CircuitMonkey/epoch-3/Firmware/epoch-3-fw/glyphs.h

#include <sys/_stdint.h>
// [glyph16g]  glyph  16x16   greyscale  as nybles
#ifndef Glyphs_h 
#define Glyphs_h

#define LOGO_W 128
#define LOGO_H 88
#define GLYPH_WH 64

#define PROGMEM

const uint8_t logo[] PROGMEM = { // 128 x 88 1-bit logo
  0x00,0x00,0x00,0x00,0x00,0x00,0x00,0x00,0x00,0x00,0x00,0x00,0x00,0x00,0x00,0x00
  ,0x00,0x00,0x00,0x00,0x00,0x00,0x00,0x00,0x00,0x00,0x00,0x00,0x00,0x00,0x00,0x00
  ,0x00,0x00,0x00,0x00,0x00,0x00,0x00,0x00,0x00,0x00,0x00,0x00,0x00,0x00,0x00,0x00
  ,0x00,0x00,0x00,0x00,0x00,0x00,0x00,0x00,0x00,0x00,0x00,0x00,0x00,0x00,0x00,0x00
  ,0x00,0x00,0x00,0x00,0x00,0x00,0x00,0x00,0x00,0x00,0x00,0x00,0x00,0x00,0x00,0x00
  ,0x00,0x00,0x00,0x00,0x00,0x00,0x00,0x00,0x00,0x00,0x00,0x00,0x00,0x00,0x00,0x00
  ,0x00,0x00,0x00,0x00,0x00,0x00,0x00,0x00,0x00,0x00,0x00,0x00,0x00,0x00,0x00,0x00
  ,0x00,0x00,0x00,0x00,0x00,0x00,0x00,0x00,0x00,0x00,0x00,0x00,0x00,0x00,0x00,0x00
  ,0x00,0x00,0x00,0x00,0x00,0x00,0x00,0x00,0x00,0x00,0x00,0x00,0x00,0x00,0x00,0x00
  ,0x00,0x00,0x00,0x00,0x00,0x00,0x00,0x00,0x00,0x00,0x00,0x00,0x00,0x00,0x00,0x00
  ,0x00,0x00,0x00,0x00,0x00,0x00,0x00,0x00,0x00,0x00,0x00,0x00,0x00,0x00,0x00,0x00
  ,0x00,0x00,0x00,0x00,0x00,0x00,0x00,0x00,0x00,0x00,0x00,0x00,0x00,0x00,0x00,0x00
  ,0x00,0x00,0x00,0x00,0x00,0x00,0x00,0x00,0x00,0x00,0x00,0x00,0x00,0x00,0x00,0x00
  ,0x00,0x00,0x00,0x00,0x00,0x00,0x00,0x00,0x00,0x00,0x00,0x00,0x00,0x00,0x00,0x00
  ,0x00,0x00,0x00,0x00,0x00,0x00,0x00,0x00,0x00,0x00,0x00,0x00,0x00,0x00,0x00,0x00
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
  ,0xf0,0x00,0x03,0xff,0x7f,0xff,0xf8,0x0f
  ,0xf0,0x00,0x00,0xff,0x1f,0xff,0xfc,0x0f
  ,0xf0,0x00,0xff,0xff,0xff,0xff,0xfc,0x0f
  ,0xf0,0x00,0xff,0xff,0xff,0xff,0xfc,0x0f
  ,0xf0,0x00,0xff,0x18,0x1c,0xff,0xfc,0x0f
  ,0xf0,0x00,0xff,0x38,0x38,0x3f,0xf8,0x0f
  ,0xf0,0x00,0x00,0x70,0x38,0x1f,0xf0,0x0f
  ,0xf0,0x00,0x00,0x60,0x70,0x07,0xf0,0x0f
  ,0xf0,0x00,0x00,0xe0,0xe0,0x01,0xe0,0x0f
  ,0xf0,0x00,0x01,0xc0,0xc0,0x00,0x00,0x0f
  ,0xf0,0x00,0x01,0x81,0xc0,0x00,0x00,0x0f
  ,0xf0,0x00,0x03,0x83,0x80,0x00,0x00,0x0f
  ,0xf0,0x00,0x07,0x03,0x00,0x00,0x00,0x0f
  ,0xf0,0x00,0x06,0x07,0x00,0x00,0x00,0x0f
  ,0xf0,0x00,0x0e,0x0e,0x00,0x00,0x00,0x0f
  ,0xf0,0x00,0x1c,0x0c,0x00,0x00,0x00,0x0f
  ,0xf0,0x00,0x38,0x1c,0x00,0x00,0x00,0x0f
  ,0xf0,0x00,0x38,0x38,0x00,0x00,0x00,0x0f
  ,0xf0,0x00,0x70,0x30,0x00,0x00,0x00,0x0f
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
};
#endif
